MarkTA/PocketLab/docs/Component Reference/AD9833-WaveGen/PocketLab_AD9833_Oscilloscope_Test_Results.docx

PocketLab AD9833 Waveform Test Results

Analog Discovery Kit oscilloscope measurements of raw AD9833 output

Hardware: ESP32 NodeMCU-32S + AD9833 module | MCLK: 25 MHz | Supply: 3.3 V

7/12/26

Waveform | Set Frequency | Measured Frequency | Maximum | Minimum | Average | Peak-to-Peak | Observation
Sine | 100 Hz | 100.02 Hz | 0.64039 V | 0.042138 V | 0.34109 V | 0.59825 V | Clean low-frequency sine; stable bias and amplitude.
Sine | 1 kHz | 999.96 Hz | 0.64094 V | 0.041034 V | 0.34095 V | 0.59990 V | Baseline raw AD9833 DAC output.
Sine | 1 MHz | 1.0001 MHz | 0.64046 V | 0.041349 V | 0.34138 V | 0.59912 V | Amplitude remains essentially unchanged at 1 MHz.
Triangle | 1 kHz | 999.92 Hz | 0.64070 V | 0.041744 V | 0.34099 V | 0.59896 V | Matches sine-path amplitude and DC bias closely.
Triangle | 100 kHz | 99.937 kHz | 0.64267 V | 0.040718 V | 0.34107 V | 0.60195 V | Clean triangle with no meaningful amplitude loss.
Triangle | 1 MHz | 999.96 kHz | 0.61901 V | 0.050814 V | 0.34058 V | 0.56820 V | Visible rounding and modest amplitude reduction at high frequency.
Square | 1 kHz | 999.97 Hz | 2.5847 V | -0.011574 V | 1.0205 V | 2.5962 V | Digital-output path; higher amplitude than sine/triangle.
Square | 100 kHz | 100.00 kHz | 3.9042 V | -0.57510 V | 1.6531 V | 4.4793 V | Peak readings include overshoot/undershoot and edge ringing.
Square | 1 MHz | 1.0000 MHz | 3.7976 V | -0.51484 V | 1.5918 V | 4.3124 V | Strong ringing after transitions; frequency remains accurate.

Key findings

• Sine and triangle outputs use the AD9833 DAC path and are approximately 0.60 Vpp centered near 0.341 V.

• The sine amplitude remained nearly constant from 100 Hz through 1 MHz.

• Triangle amplitude stayed near 0.60 Vpp through 100 kHz, then decreased to 0.568 Vpp at 1 MHz as the shape rounded.

• Square output uses the digital path and has a much larger nominal swing than sine or triangle.

• Square-wave maximum, minimum, and peak-to-peak readings at 100 kHz and 1 MHz include overshoot, undershoot, and ringing from the fast edges and test setup.

• Measured frequency remained highly accurate across all tested settings.

Note: Values were transcribed from the WaveForms measurement panels shown during testing. Square-wave peak values reflect transient ringing and should not be interpreted as the steady-state logic levels.

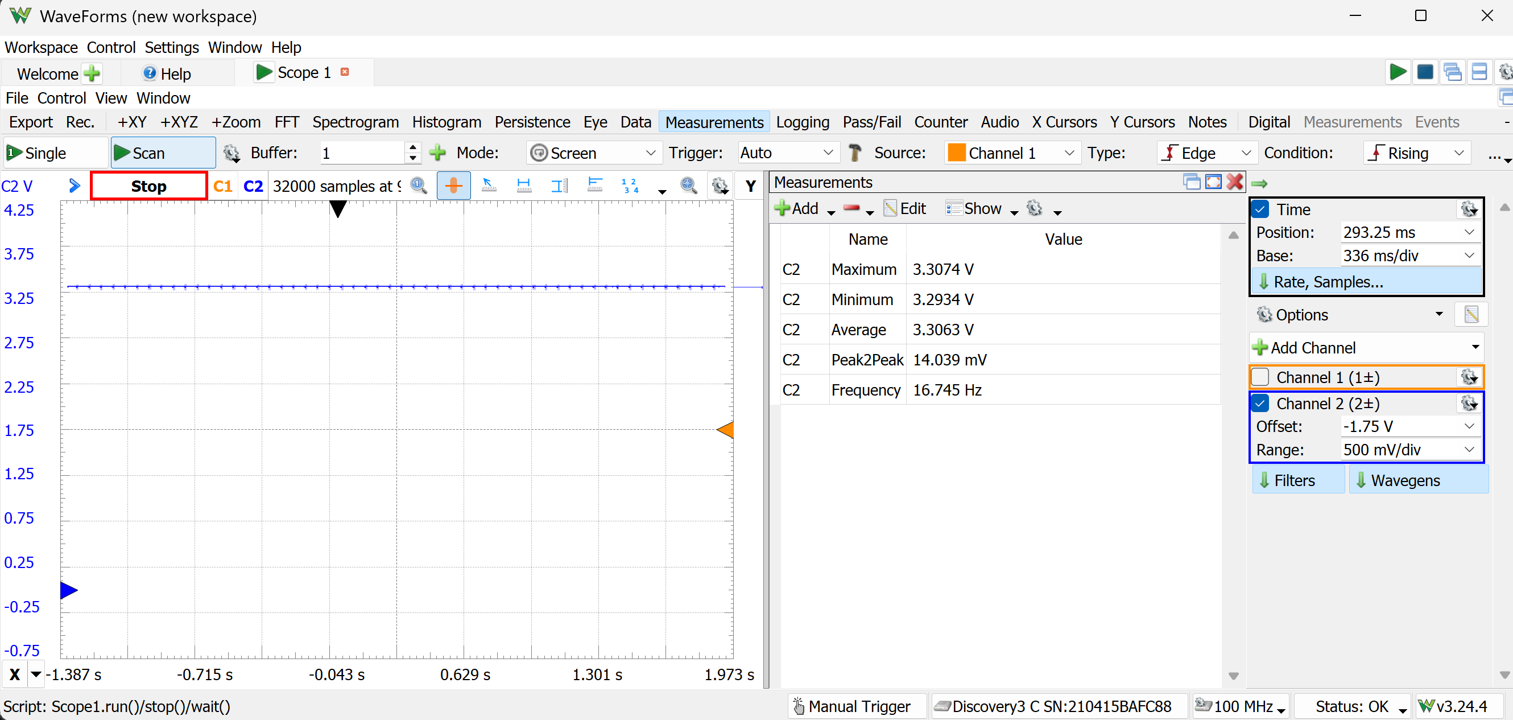
[picture p36: figure]
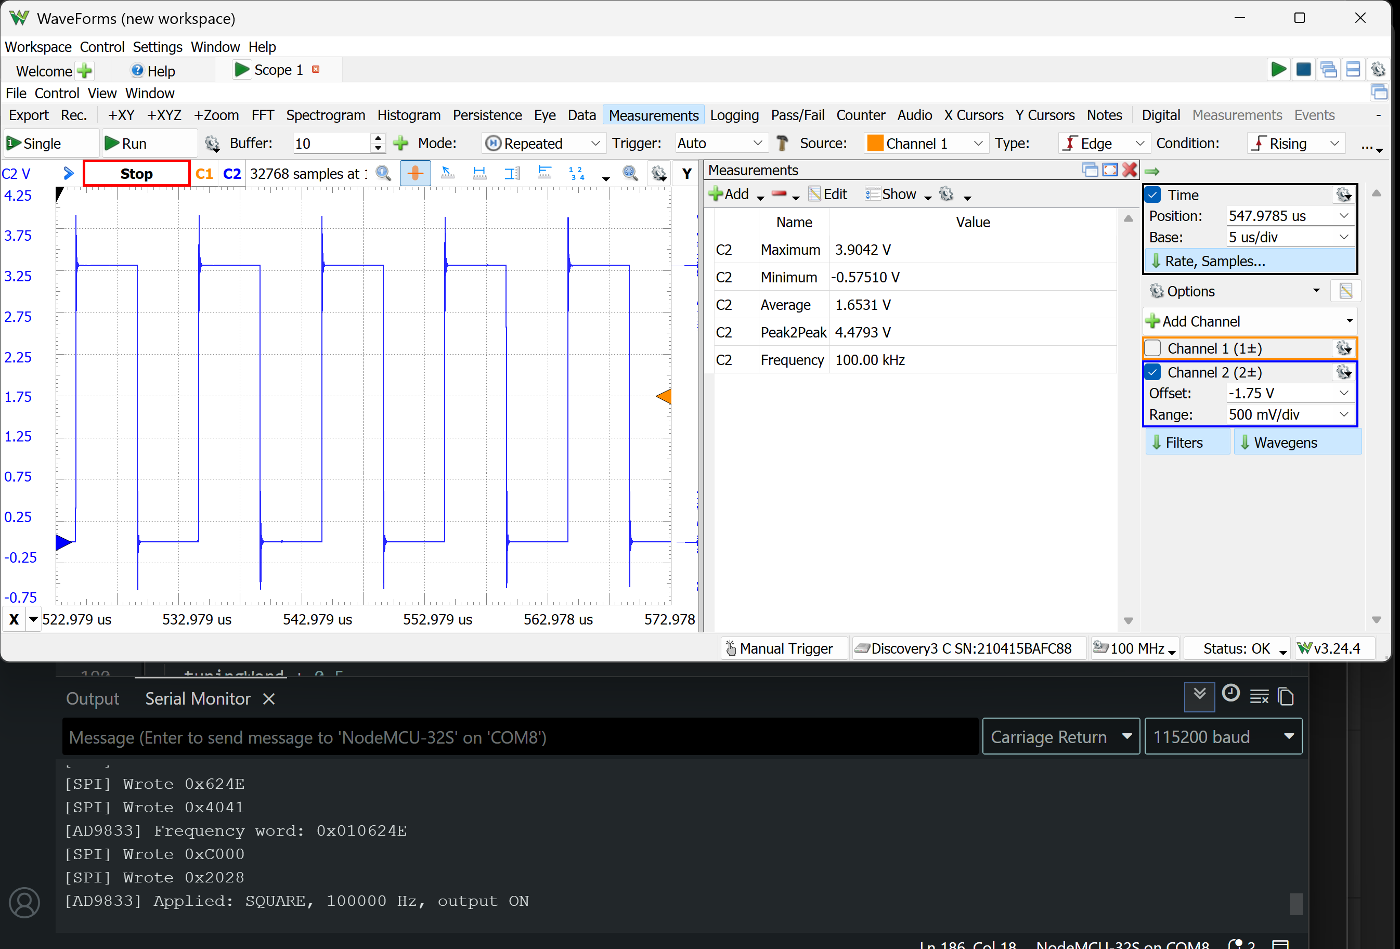
[picture p37: figure]
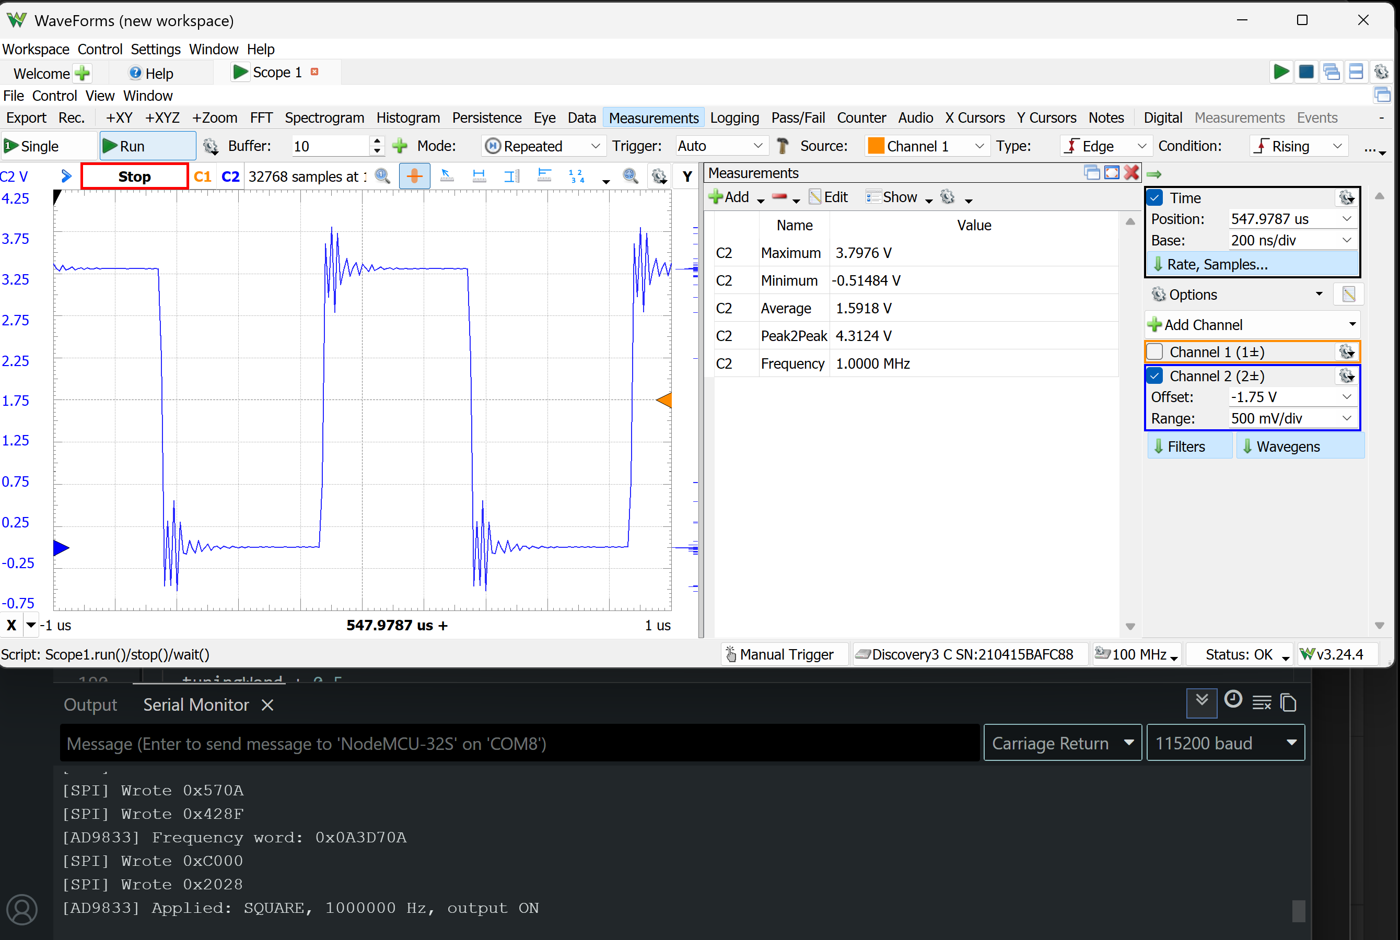
[picture p38: figure]
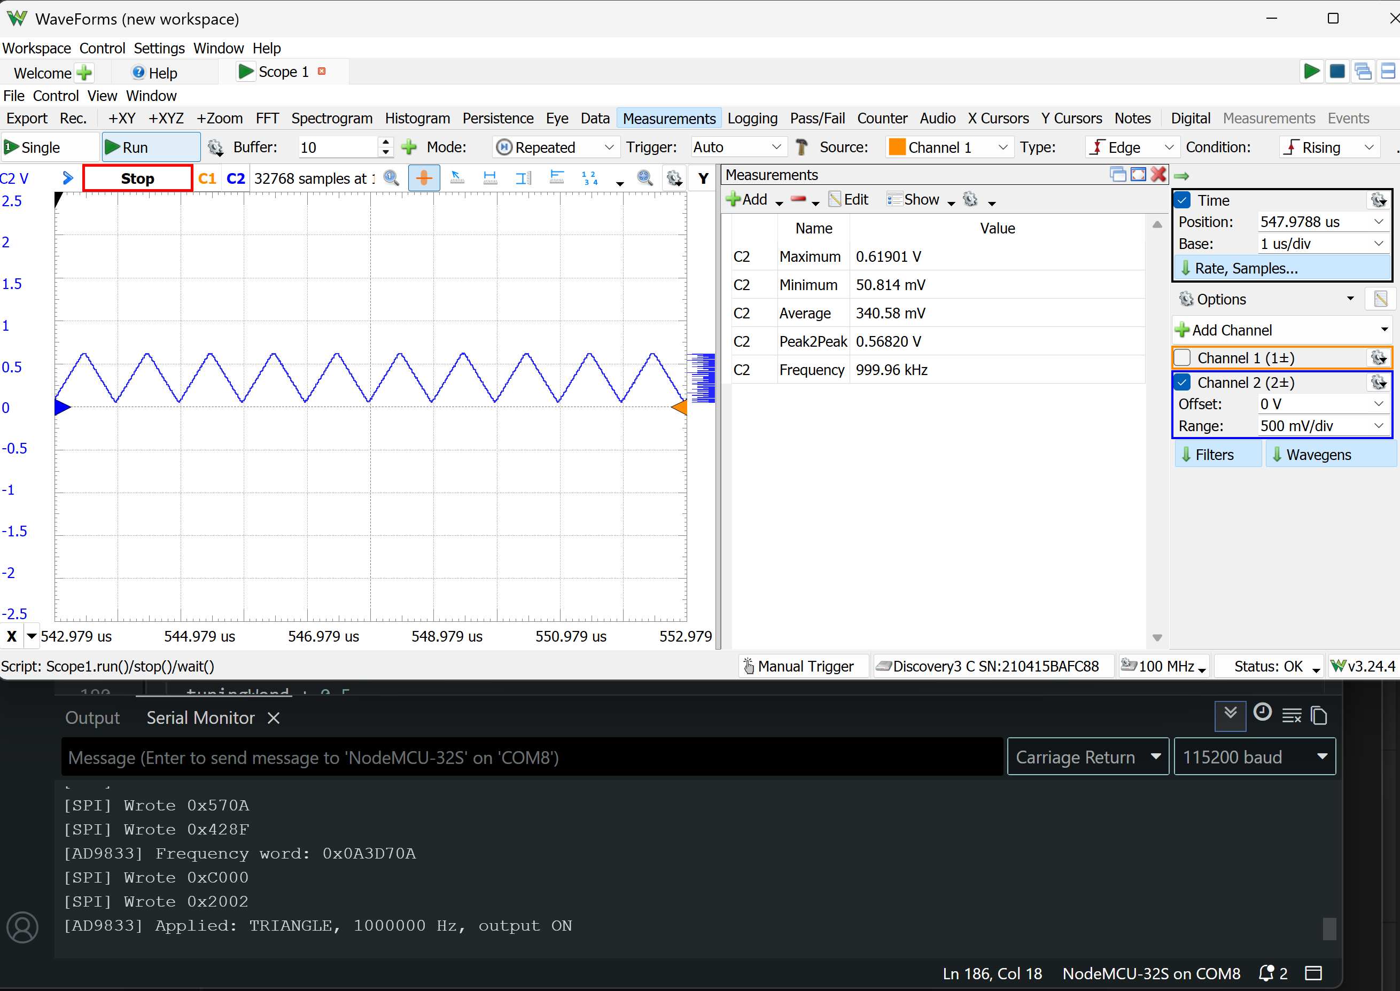
[picture p39: figure]
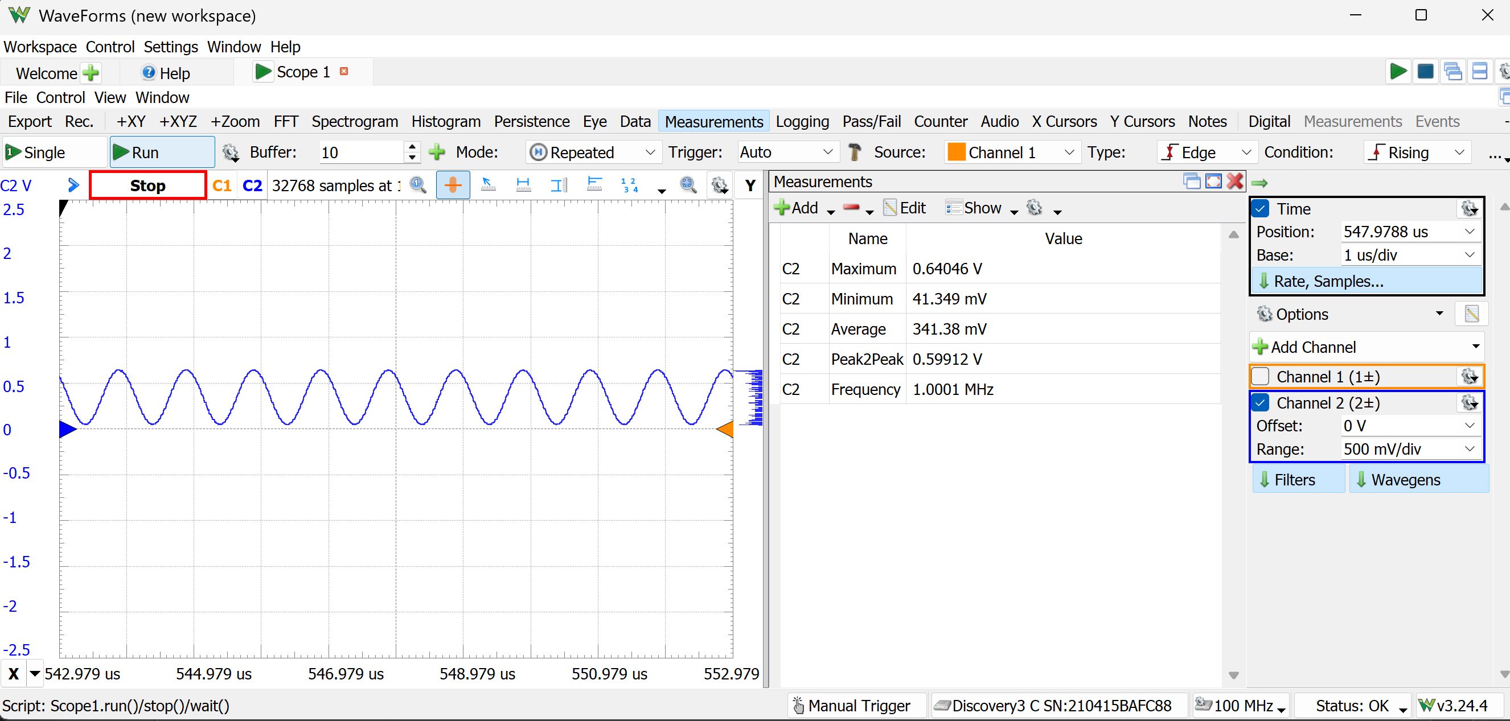
[picture p40: figure]
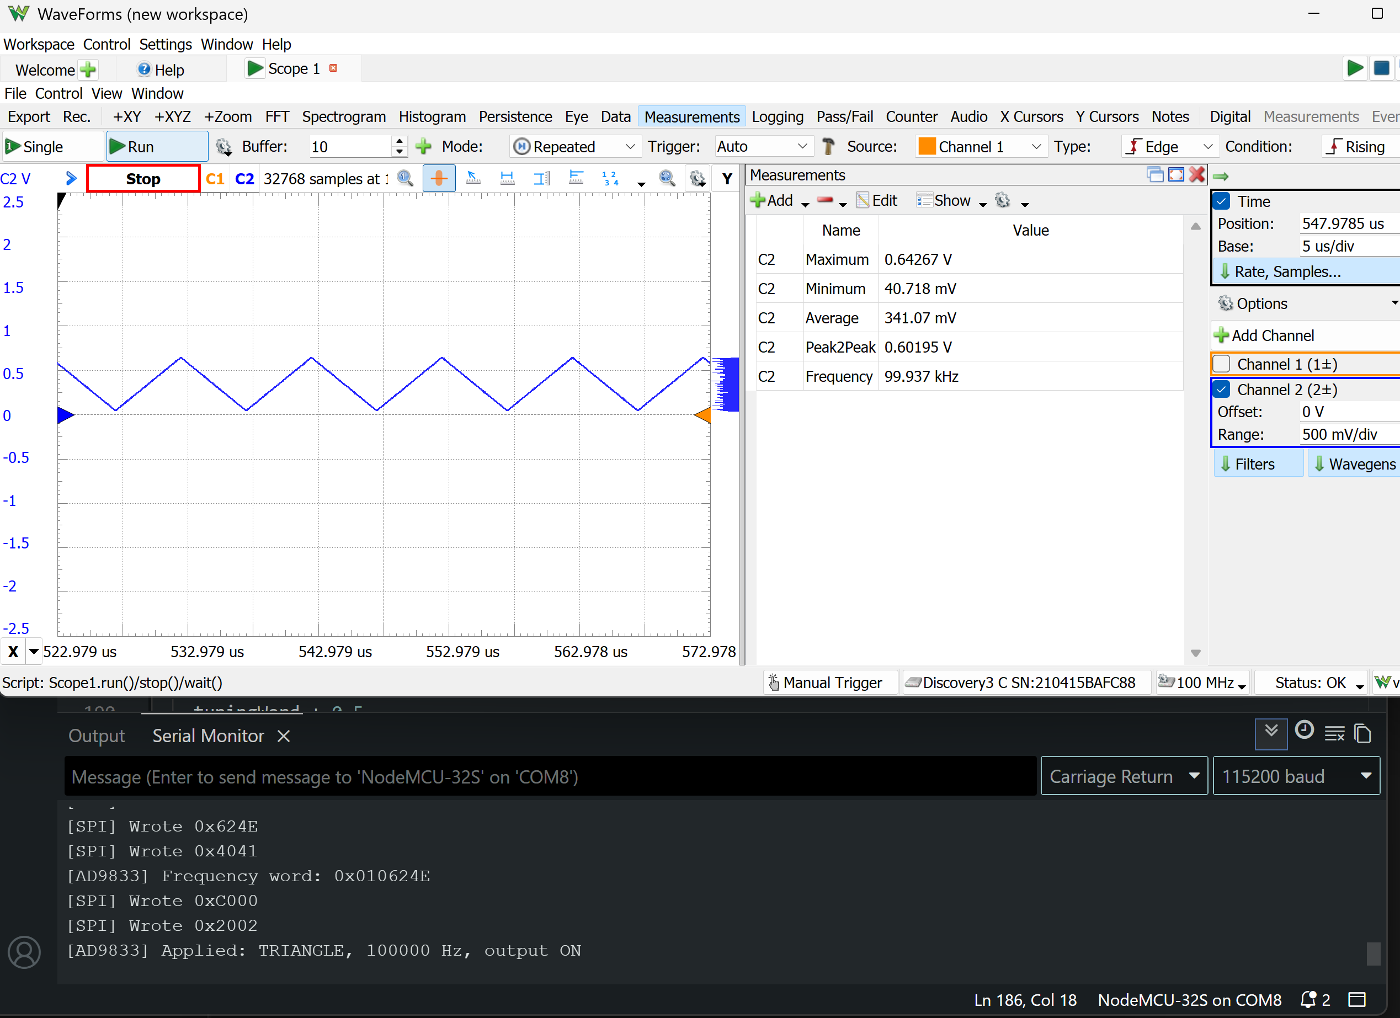
[picture p41: figure]
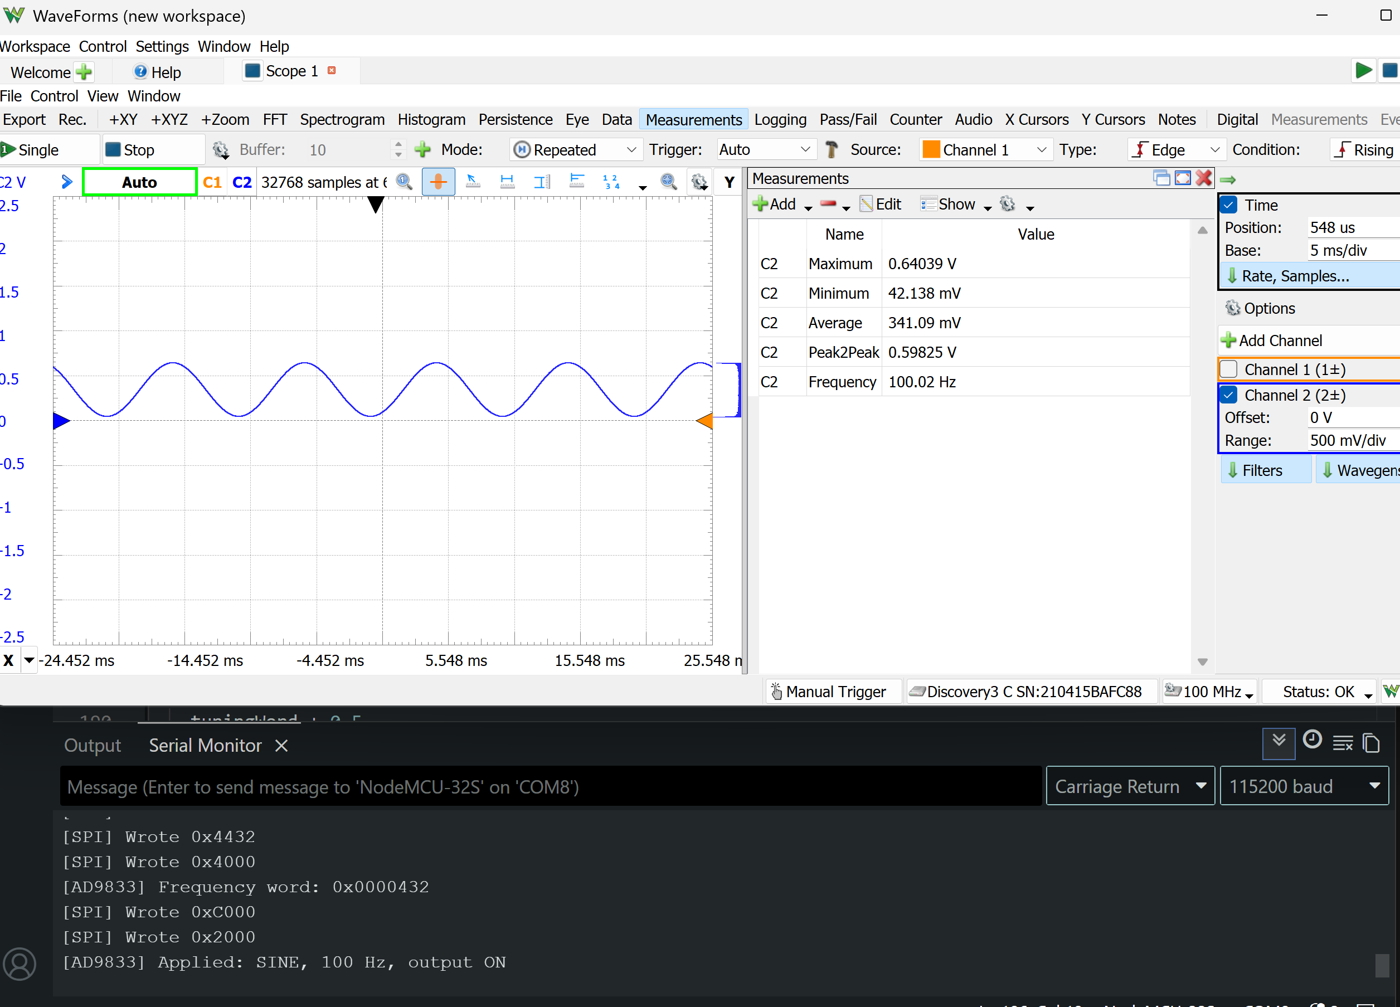
[picture p42: figure]
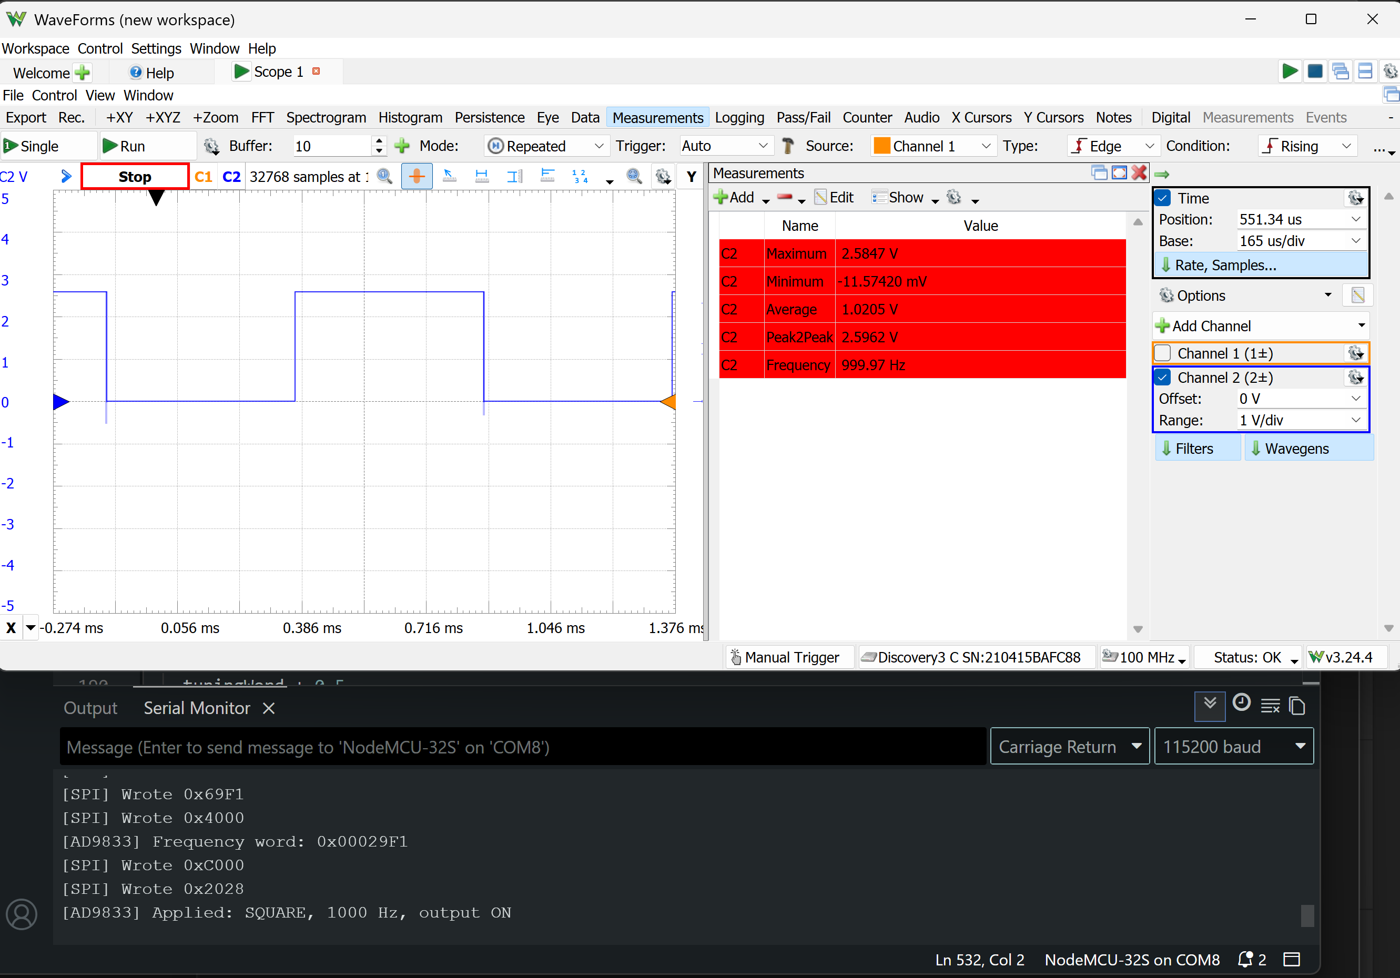
[picture p43: figure]
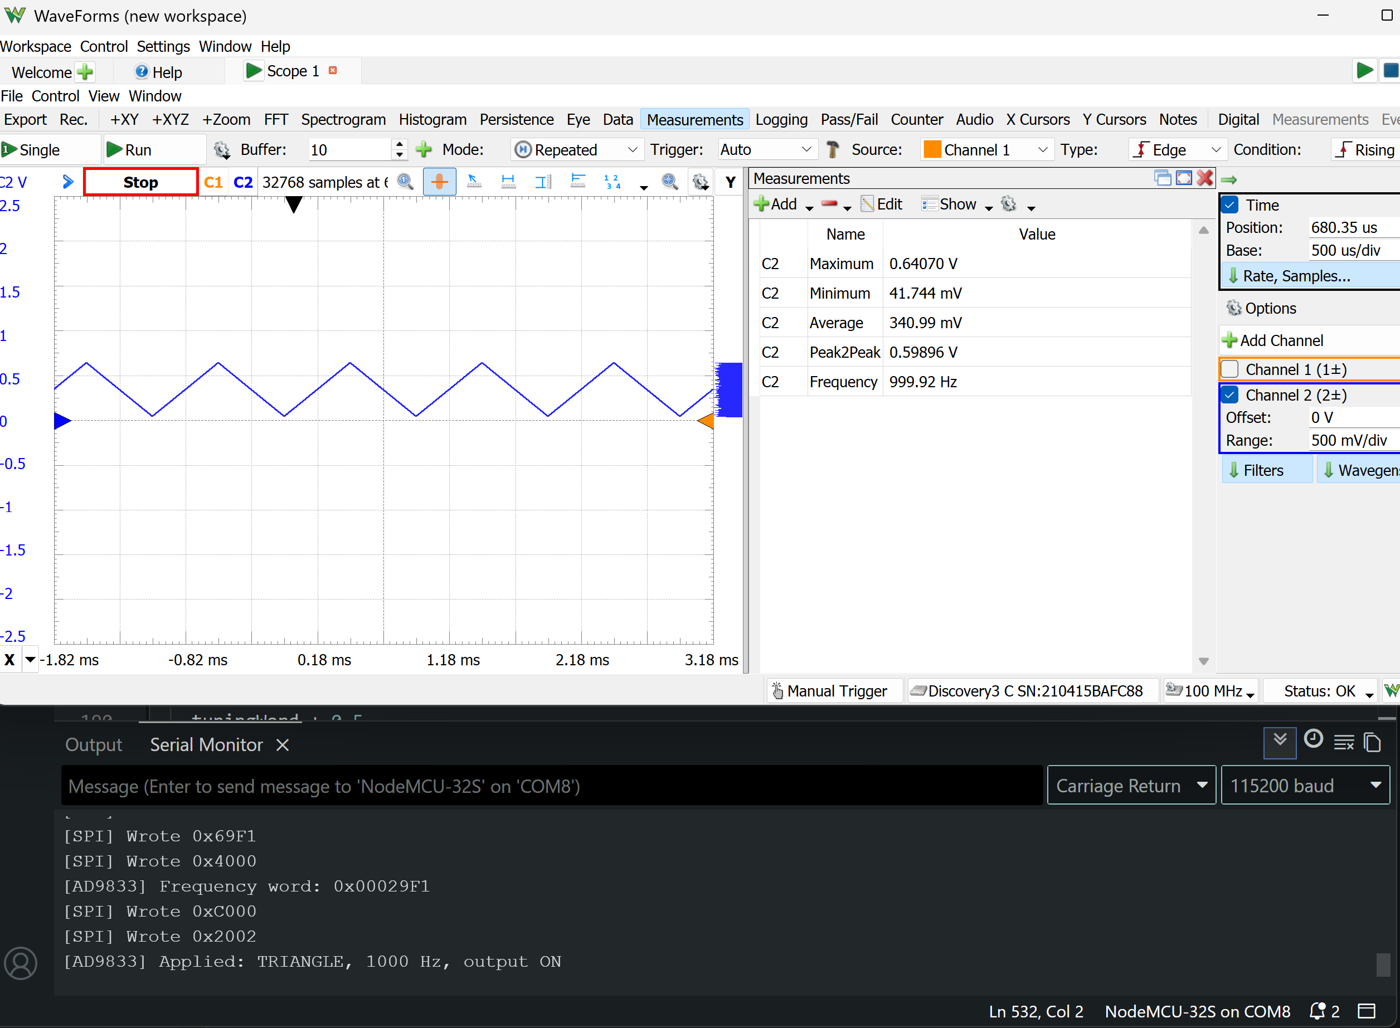
[picture p44: figure]
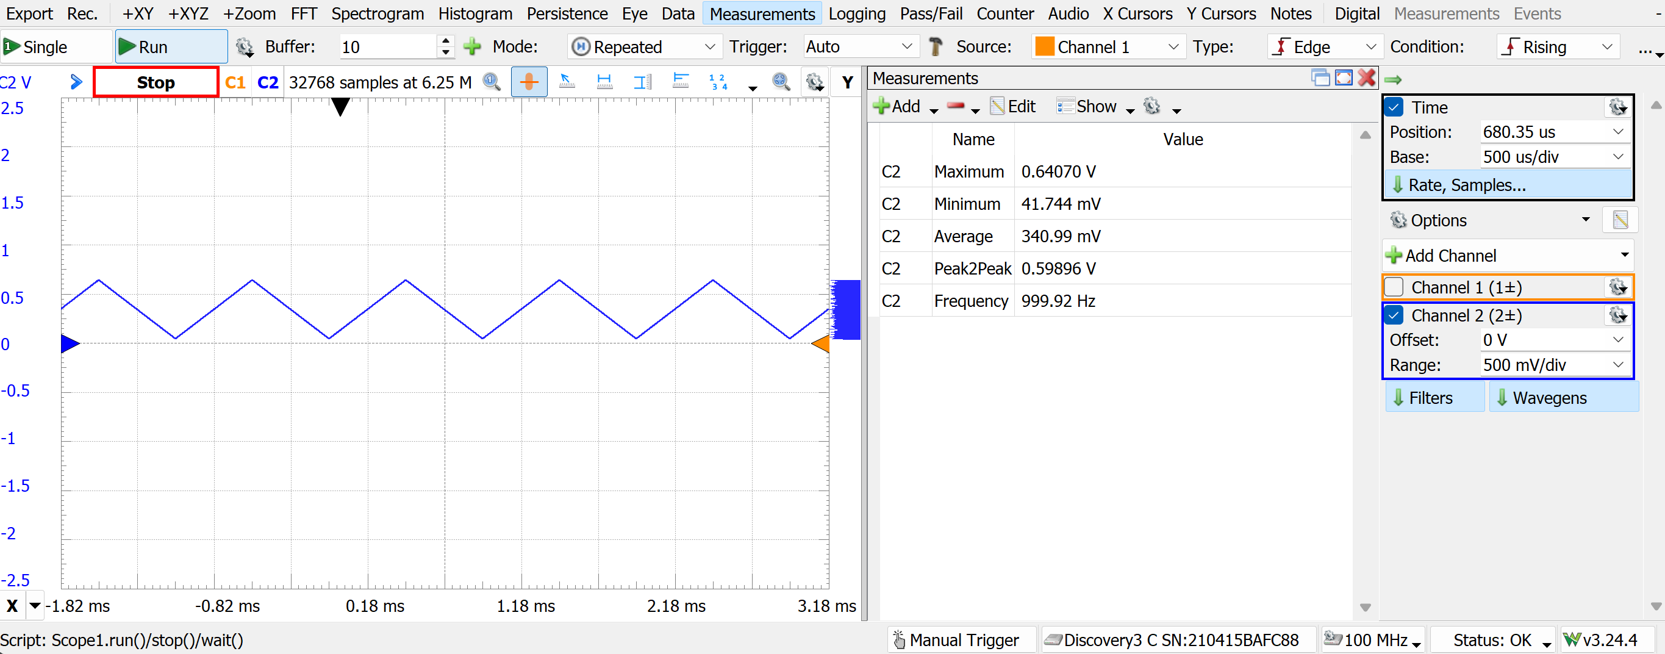
[picture p45: figure]
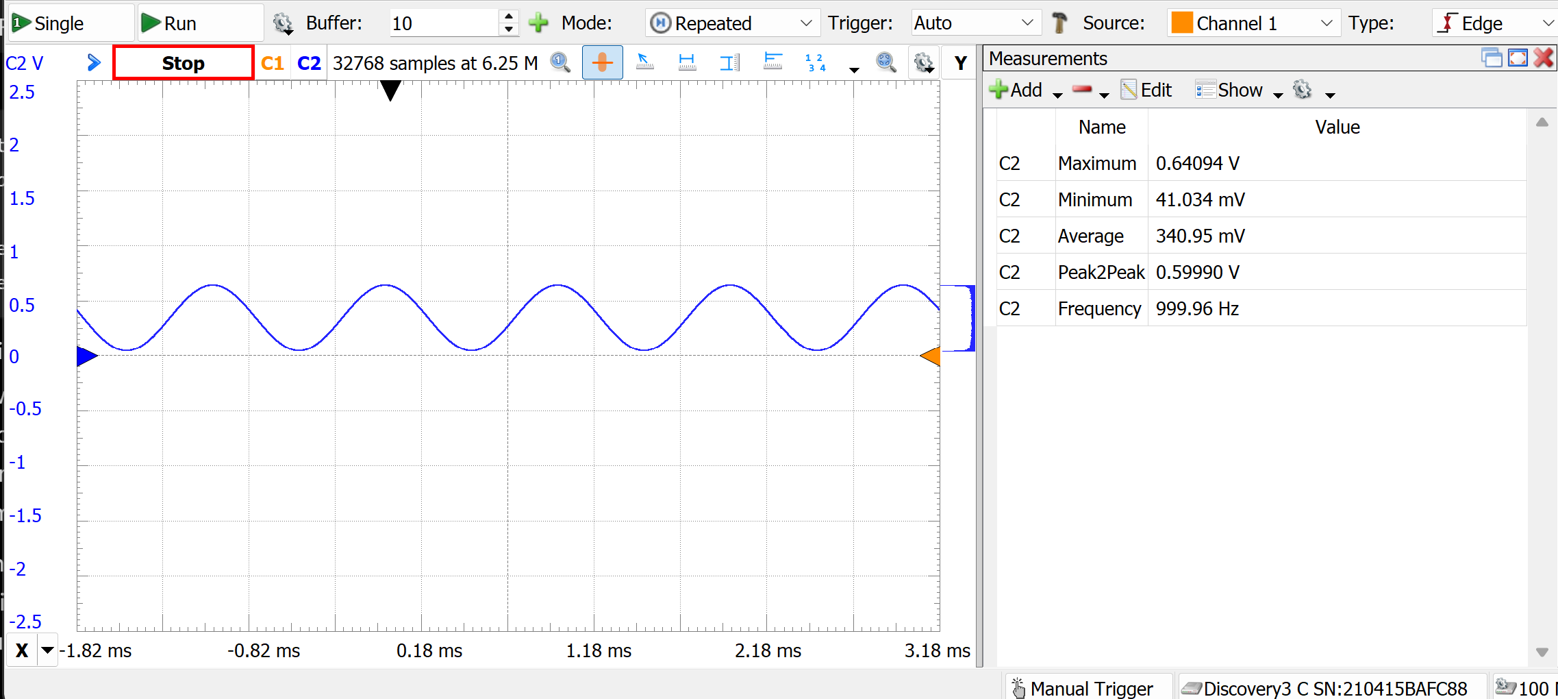
[picture p46: figure]
