MarkTA/PocketLab/docs/Circuit Test Results/PocketLab_Amplitude_Offset_Interaction_Test_Matrix.csv

Test_ID | Test_Description | Waveform | Frequency_Hz | Requested_Amplitude_Vpp | Requested_Offset_V | Calculated_Min_V | Calculated_Max_V | Expected_Result | Actual_Result | Measured_Vpp | Measured_Mean_V | Measured_Min_V | Measured_Max_V | Clipping_or_Notes
1 | Low amplitude near minimum offset | SINE | 1000 | 0.50 | 0.46 | 0.210 | 0.710 | ACCEPTED
2 | Low amplitude near maximum offset | SINE | 1000 | 0.50 | 4.14 | 3.890 | 4.390 | ACCEPTED
3 | Medium amplitude at low offset | SINE | 1000 | 2.00 | 1.25 | 0.250 | 2.250 | ACCEPTED
4 | Medium amplitude at center offset | SINE | 1000 | 2.00 | 2.30 | 1.300 | 3.300 | ACCEPTED
5 | Medium amplitude at high offset | SINE | 1000 | 2.00 | 3.35 | 2.350 | 4.350 | ACCEPTED
6 | Maximum amplitude at envelope center | SINE | 1000 | 4.15 | 2.30 | 0.225 | 4.375 | ACCEPTED
7 | Low amplitude just outside lower envelope | SINE | 1000 | 0.50 | 0.44 | 0.190 | 0.690 | REJECTED |  |  |  |  |  | Confirm previous valid output remains unchanged
8 | Low amplitude just outside upper envelope | SINE | 1000 | 0.50 | 4.16 | 3.910 | 4.410 | REJECTED |  |  |  |  |  | Confirm previous valid output remains unchanged
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
